marctheshark3/butterfly-habitat/candidate/labeled/label-details.png

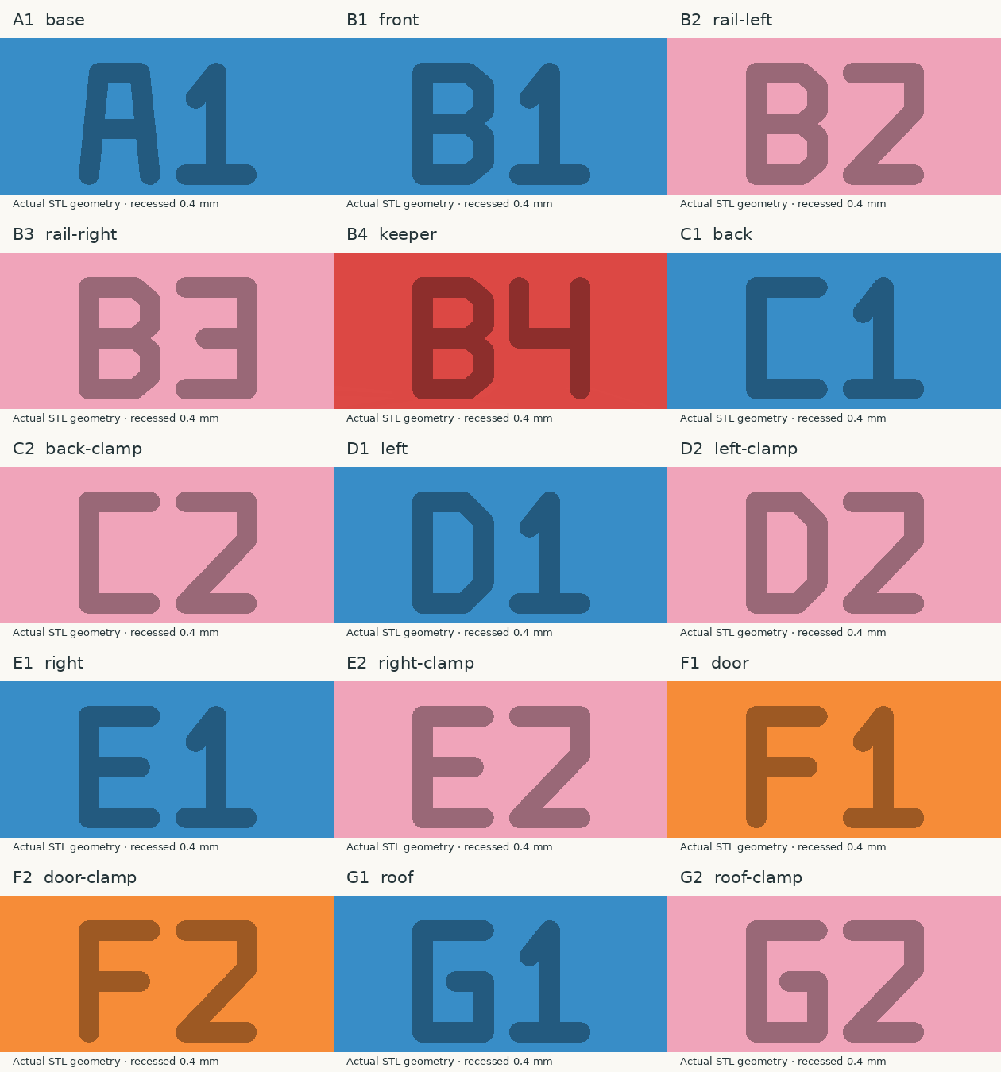
candidate/labeled/label-details.png
