marctheshark3/butterfly-habitat/candidate/slicing/habitat-left/layers.png

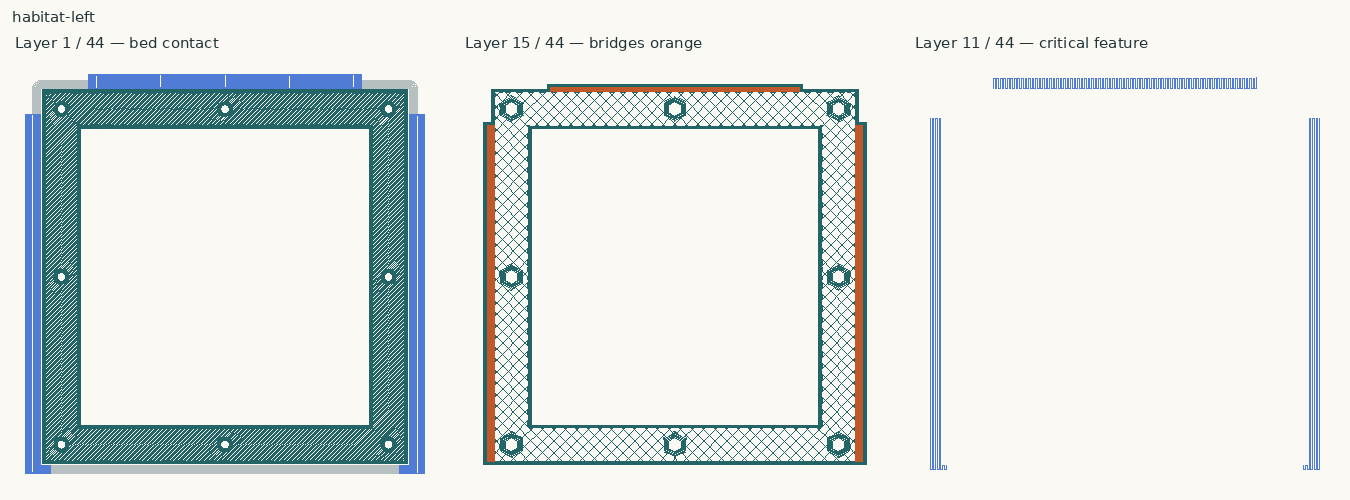
candidate/slicing/habitat-left/layers.png
