marctheshark3/butterfly-habitat/candidate/print-first/01-blue-corner-fit/01-blue-corner-fit.3mf

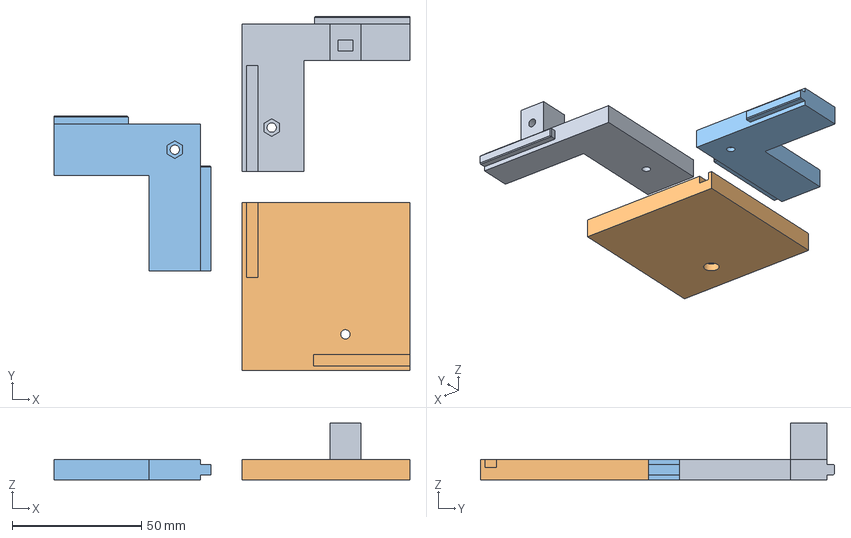
[picture p26: CAD file, 2026-10-05]
candidate/print-first/01-blue-corner-fit/01-blue-corner-fit.3mf
137.7 x 137.0 x 22.0 mm
corner-front.stl
corner-base.stl
corner-left.stl
