marctheshark3/butterfly-habitat/candidate/print-first/04-red-keeper/04-red-keeper.3mf

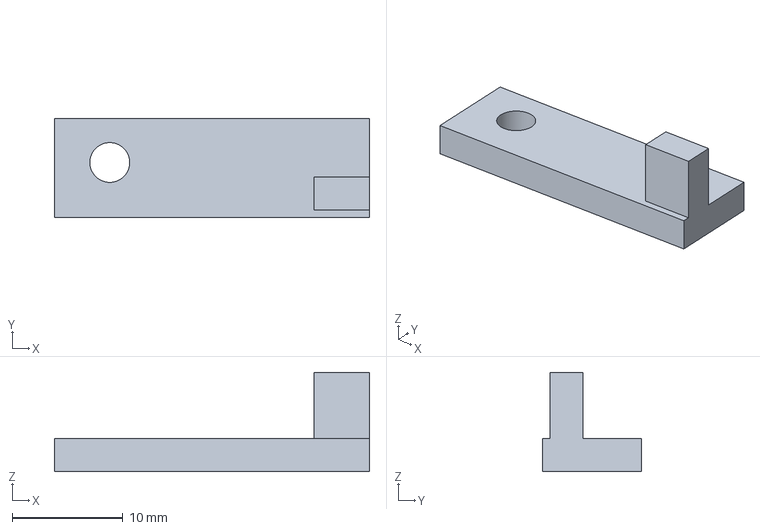
[picture p27: CAD file, 2026-10-05]
candidate/print-first/04-red-keeper/04-red-keeper.3mf
28.5 x 9.00 x 9.00 mm
