marctheshark3/butterfly-habitat/candidate/slicing/habitat-roof/sliced.3mf

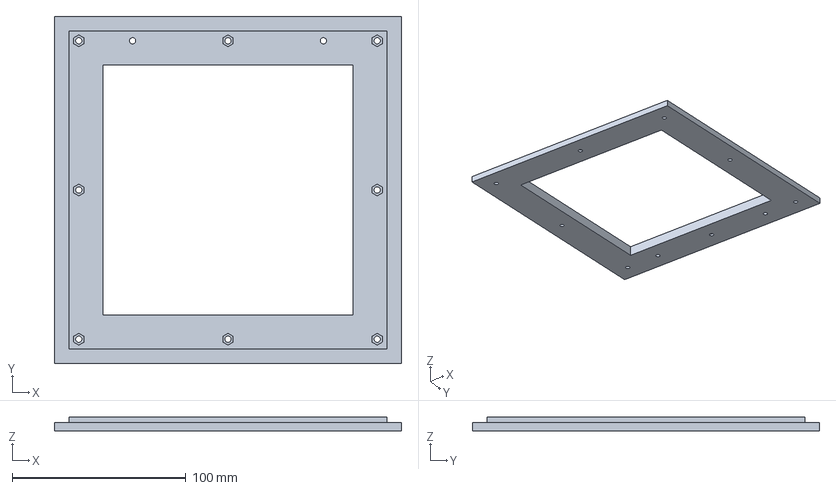
[picture p28: CAD file, 2026-10-01]
candidate/slicing/habitat-roof/sliced.3mf
200.0 x 200.0 x 8.00 mm
