marctheshark3/butterfly-habitat/step/habitat-base.step

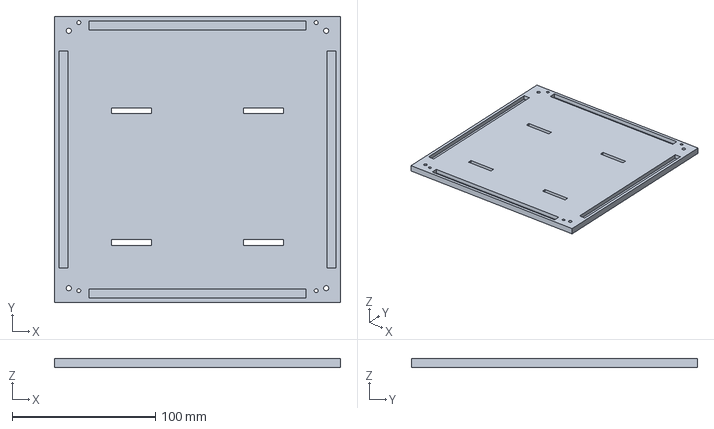
[picture p29: CAD file, 2026-10-01]
step/habitat-base.step
200.0 x 200.0 x 6.00 mm
