marctheshark3/butterfly-habitat/candidate/labeled/coupons/corner-left-clamp.step

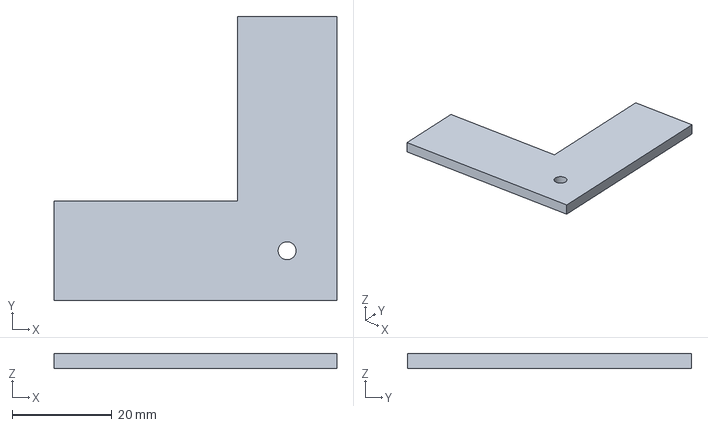
[picture p30: CAD file, 2026-10-10]
candidate/labeled/coupons/corner-left-clamp.step
56.8 x 57.0 x 3.00 mm
