marctheshark3/butterfly-habitat/step/habitat-snap-tongue-coupon.step

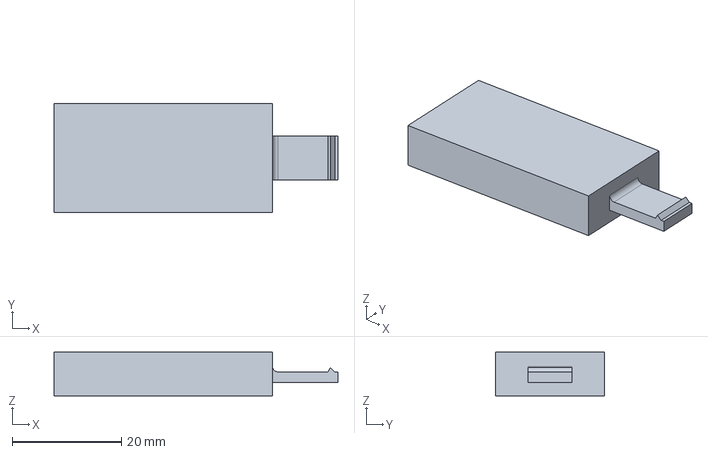
[picture p31: CAD file, 2026-10-01]
step/habitat-snap-tongue-coupon.step
52.0 x 20.0 x 8.00 mm
