marctheshark3/butterfly-habitat/candidate/labeled/coupons/mesh-fastener-back-clamp.step

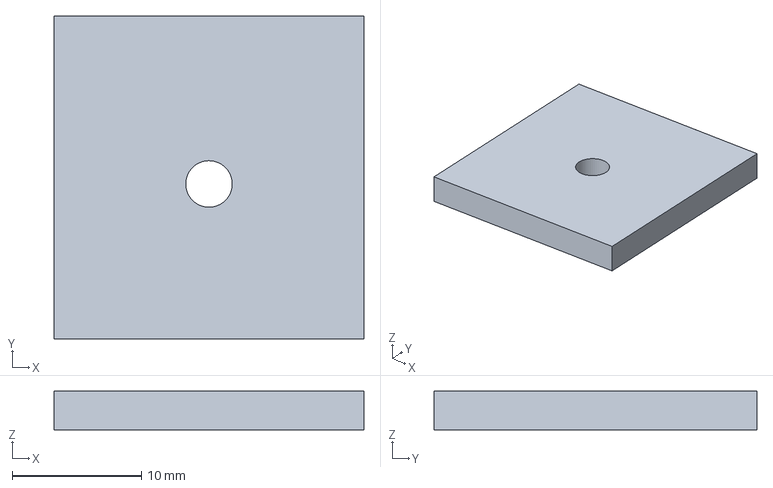
[picture p32: CAD file, 2026-10-10]
candidate/labeled/coupons/mesh-fastener-back-clamp.step
24.0 x 25.0 x 3.00 mm
