marctheshark3/butterfly-habitat/step/habitat-clamp-wall.step

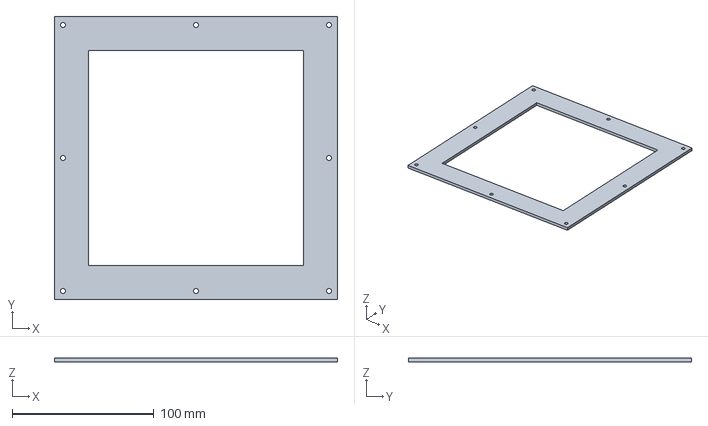
[picture p33: CAD file, 2026-10-01]
step/habitat-clamp-wall.step
200.0 x 200.0 x 3.00 mm
