marctheshark3/butterfly-habitat/candidate/labeled/coupons/corner-left.step

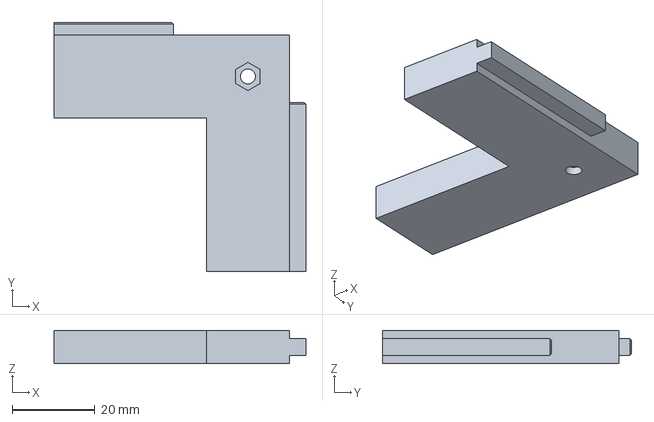
[picture p34: CAD file, 2026-10-10]
candidate/labeled/coupons/corner-left.step
60.7 x 60.0 x 8.00 mm
