marctheshark3/butterfly-habitat/step/habitat-clamp-roof.step

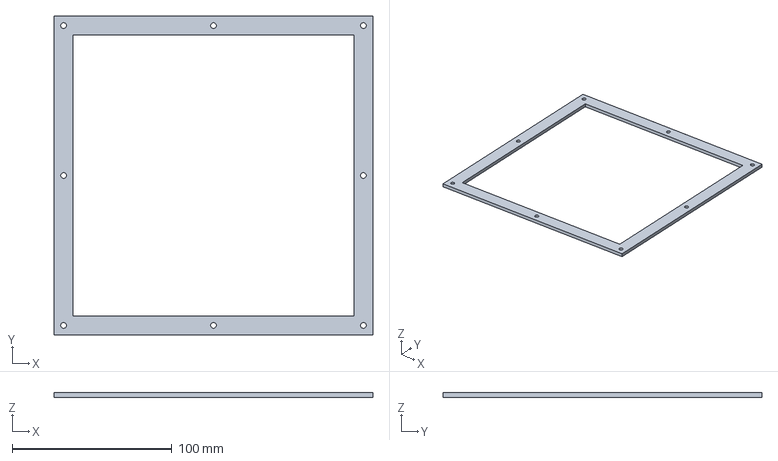
[picture p35: CAD file, 2026-10-01]
step/habitat-clamp-roof.step
200.0 x 200.0 x 3.00 mm
