marctheshark3/butterfly-habitat/candidate/labeled/coupons/rail-door-clamp.step

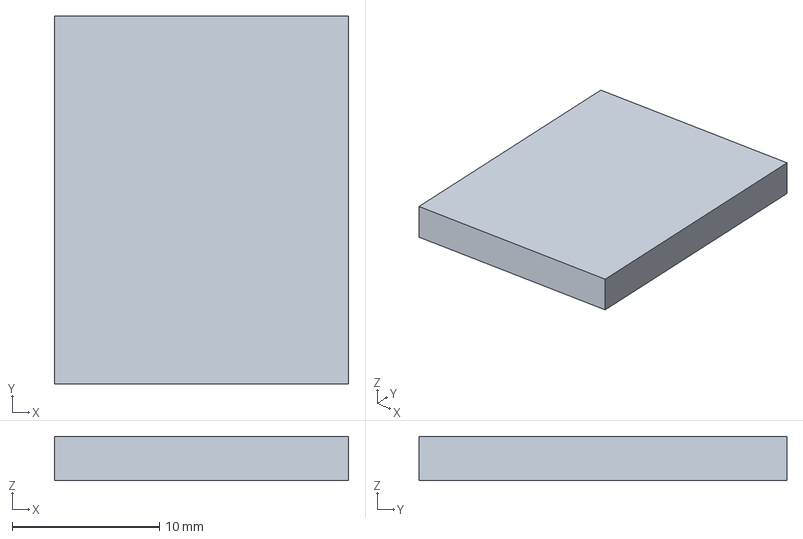
[picture p36: CAD file, 2026-10-10]
candidate/labeled/coupons/rail-door-clamp.step
20.0 x 25.0 x 3.00 mm
