marctheshark3/butterfly-habitat/step/habitat-right.step

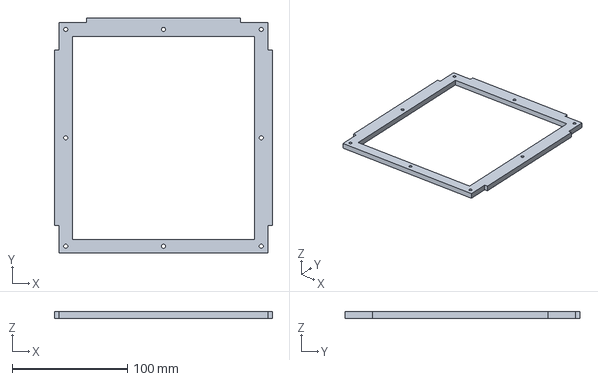
[picture p37: CAD file, 2026-10-01]
step/habitat-right.step
189.0 x 204.0 x 6.00 mm
