marctheshark3/butterfly-habitat/candidate/labeled/coupons/corner-front.step

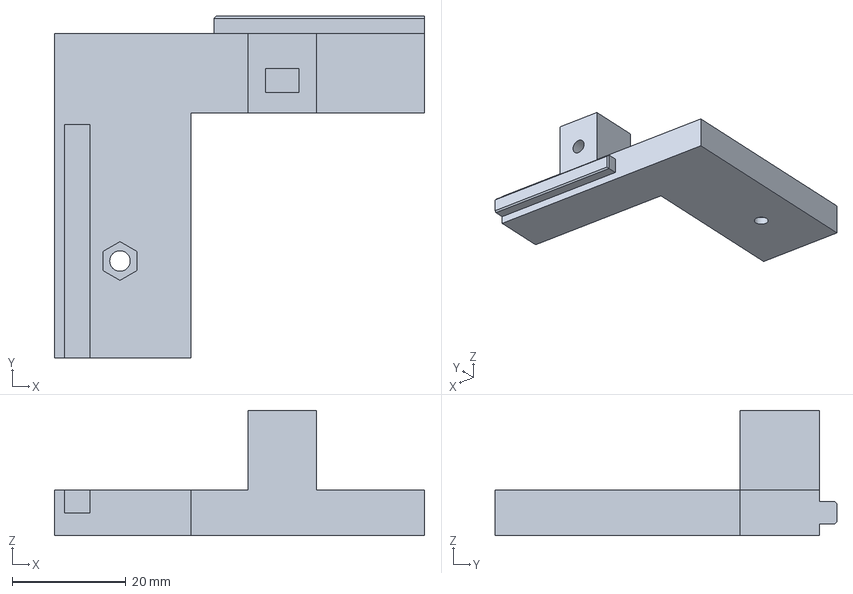
[picture p38: CAD file, 2026-10-10]
candidate/labeled/coupons/corner-front.step
65.0 x 60.0 x 22.0 mm
