marctheshark3/butterfly-habitat/step/habitat-door-frame.step

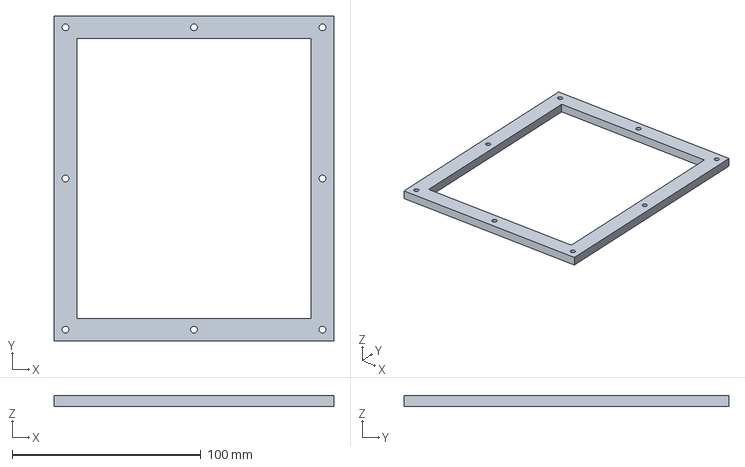
[picture p39: CAD file, 2026-10-01]
step/habitat-door-frame.step
148.0 x 172.0 x 6.00 mm
