marctheshark3/butterfly-habitat/candidate/labeled/coupons/mesh-fastener-back.step

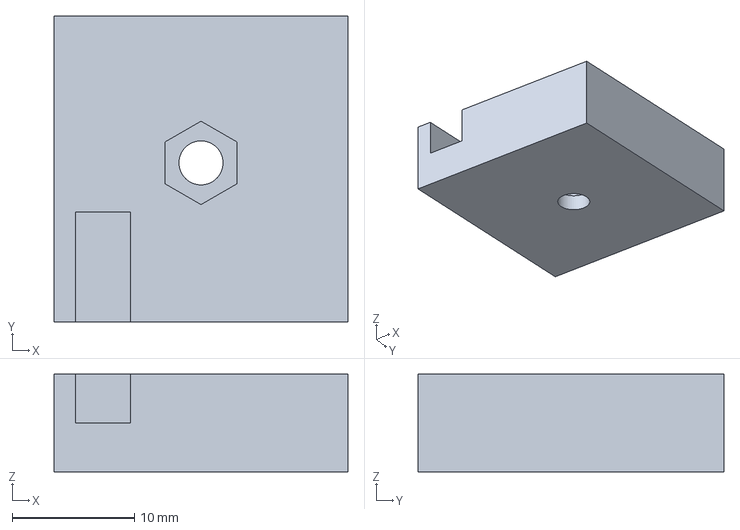
[picture p40: CAD file, 2026-10-10]
candidate/labeled/coupons/mesh-fastener-back.step
24.0 x 25.0 x 8.00 mm
