marctheshark3/butterfly-habitat/step/habitat-snap-pocket-coupon.step

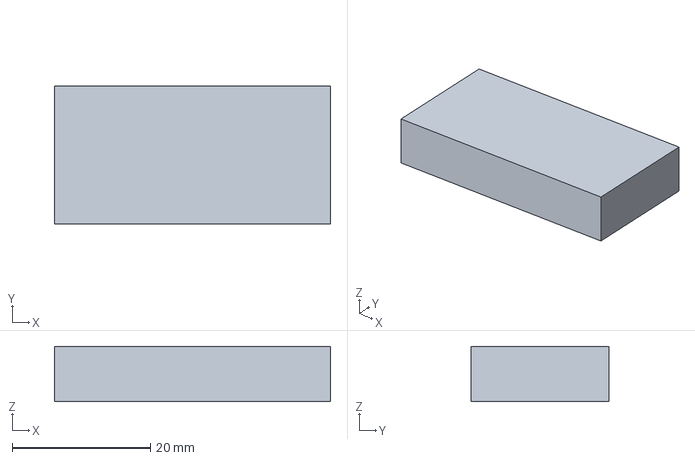
[picture p41: CAD file, 2026-10-01]
step/habitat-snap-pocket-coupon.step
40.0 x 20.0 x 8.00 mm
