marctheshark3/butterfly-habitat/candidate/labeled/coupons/rail-front.step

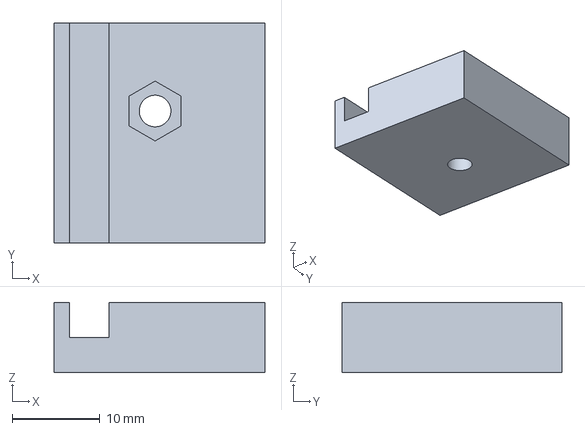
[picture p42: CAD file, 2026-10-10]
candidate/labeled/coupons/rail-front.step
24.0 x 25.0 x 8.00 mm
