marctheshark3/butterfly-habitat/step/habitat-back.step

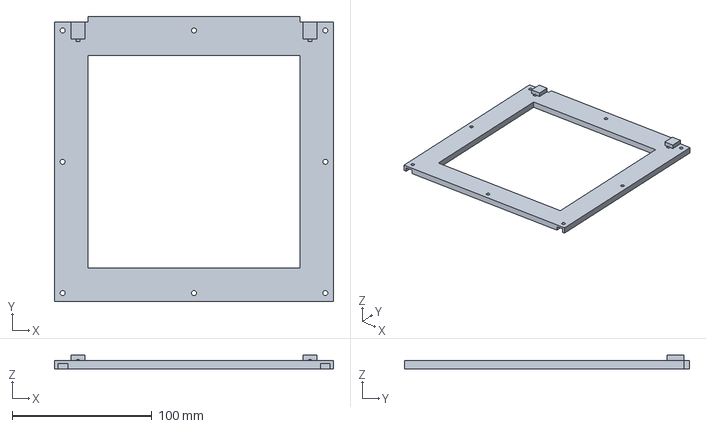
[picture p43: CAD file, 2026-10-01]
step/habitat-back.step
200.0 x 204.0 x 10.0 mm
