marctheshark3/butterfly-habitat/candidate/labeled/coupons/corner-base.step

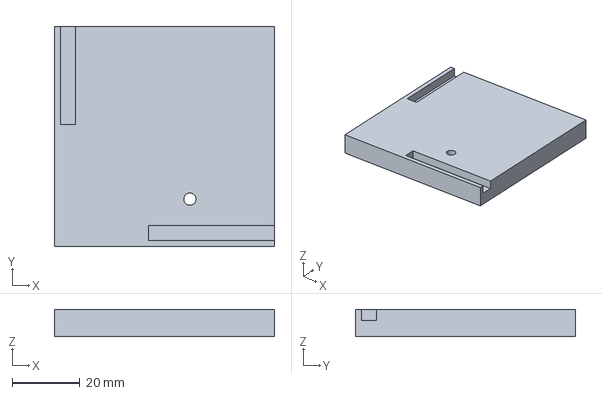
[picture p44: CAD file, 2026-10-10]
candidate/labeled/coupons/corner-base.step
65.0 x 65.0 x 8.00 mm
