marctheshark3/butterfly-habitat/step/habitat-top.step

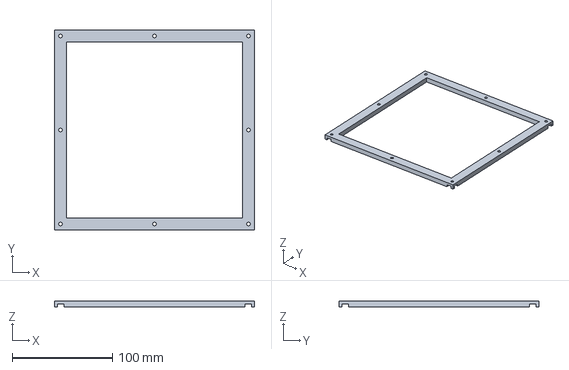
[picture p45: CAD file, 2026-10-01]
step/habitat-top.step
200.0 x 200.0 x 6.00 mm
