marctheshark3/butterfly-habitat/candidate/labeled/coupons/rail-door.step

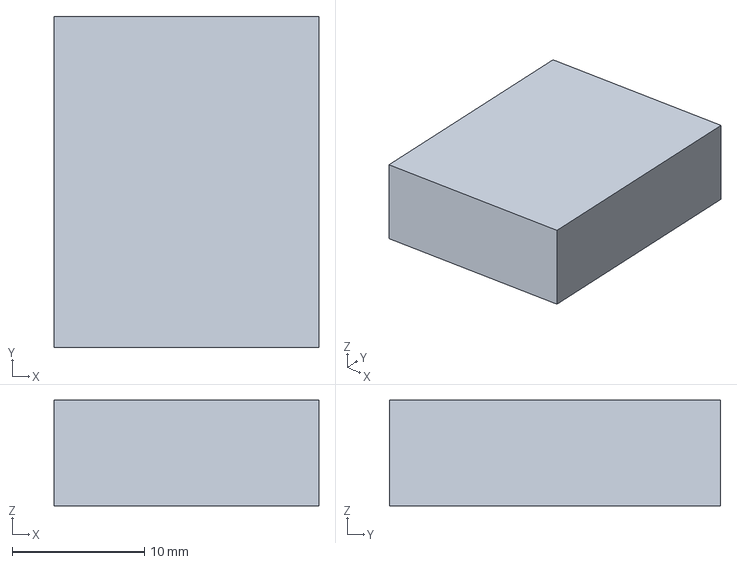
[picture p46: CAD file, 2026-10-10]
candidate/labeled/coupons/rail-door.step
20.0 x 25.0 x 8.00 mm
