marctheshark3/butterfly-habitat/step/habitat-clamp-side.step

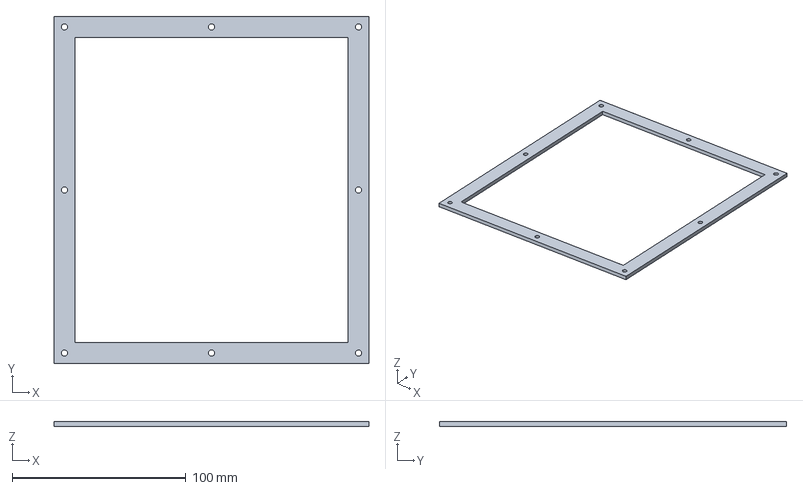
[picture p47: CAD file, 2026-10-01]
step/habitat-clamp-side.step
181.5 x 200.0 x 3.00 mm
