marctheshark3/butterfly-habitat/step/habitat-front.step

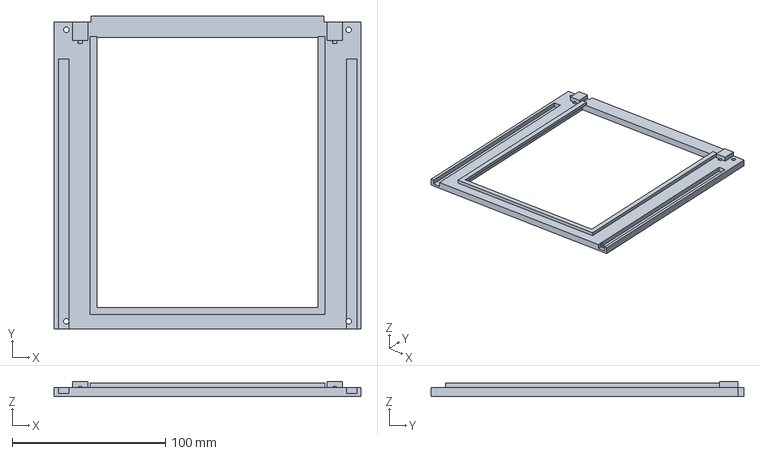
[picture p48: CAD file, 2026-10-01]
step/habitat-front.step
200.0 x 204.0 x 10.0 mm
