marctheshark3/butterfly-habitat/step/habitat-clamp-door.step

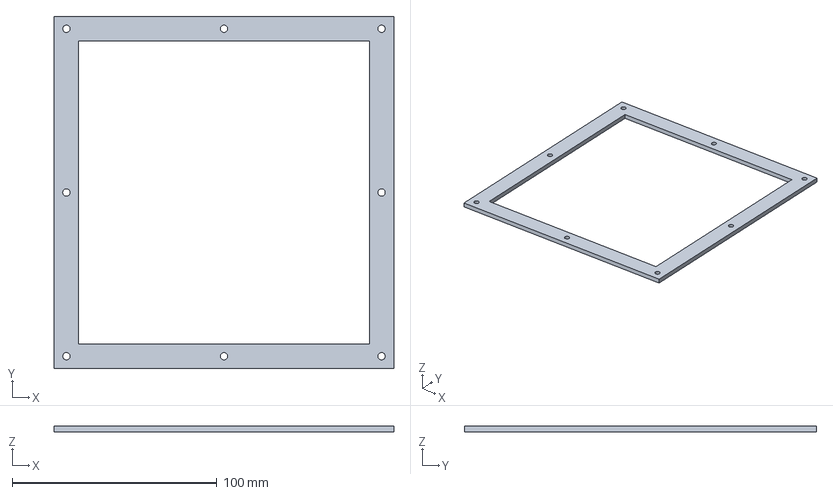
[picture p49: CAD file, 2026-09-28]
step/habitat-clamp-door.step
166.0 x 172.0 x 3.00 mm
