marctheshark3/butterfly-habitat/candidate/print-first/01-blue-corner-fit/layers.png

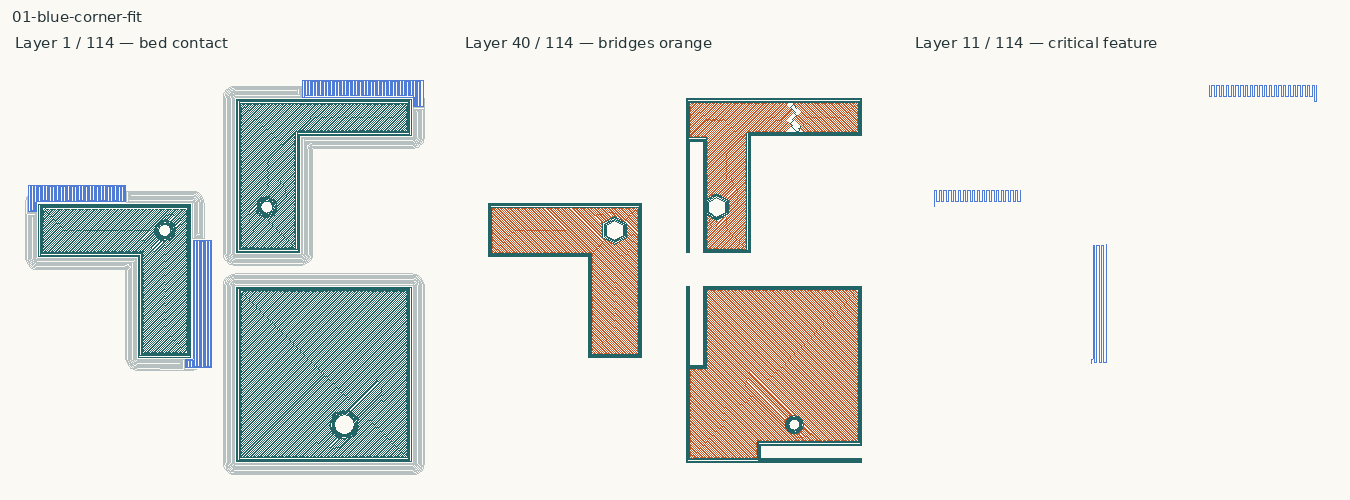
candidate/print-first/01-blue-corner-fit/layers.png
