marctheshark3/butterfly-habitat/candidate/print-first/04-red-keeper/layers.png

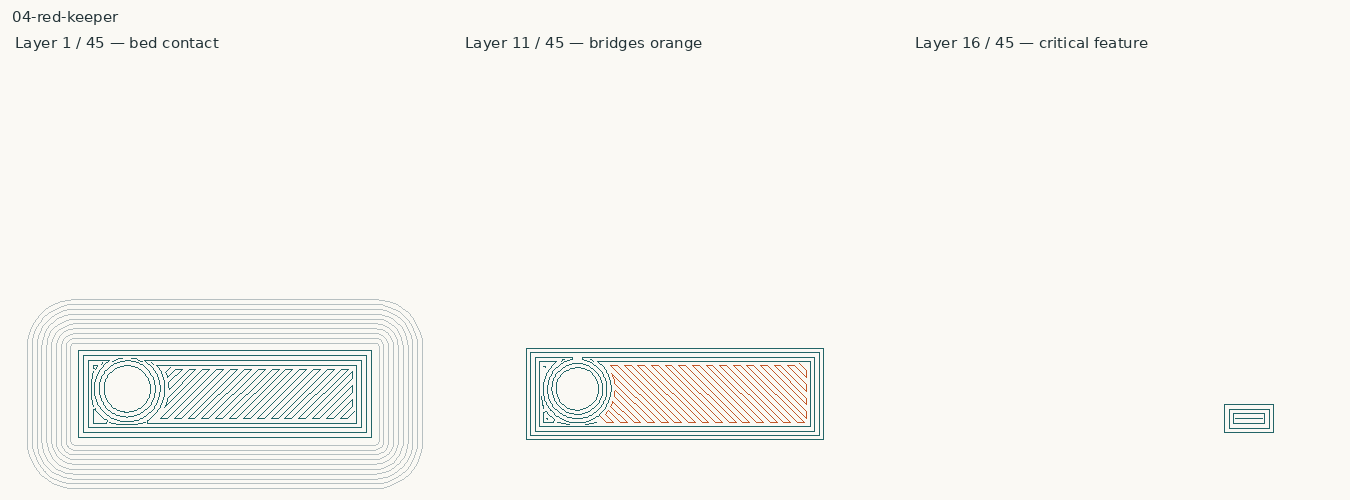
candidate/print-first/04-red-keeper/layers.png
